duivesteyn/thepricedisplay-hardwaredesign/v2021/_hardware-specification/2.9inch-e-Paper-Module-B-details-size.jpg

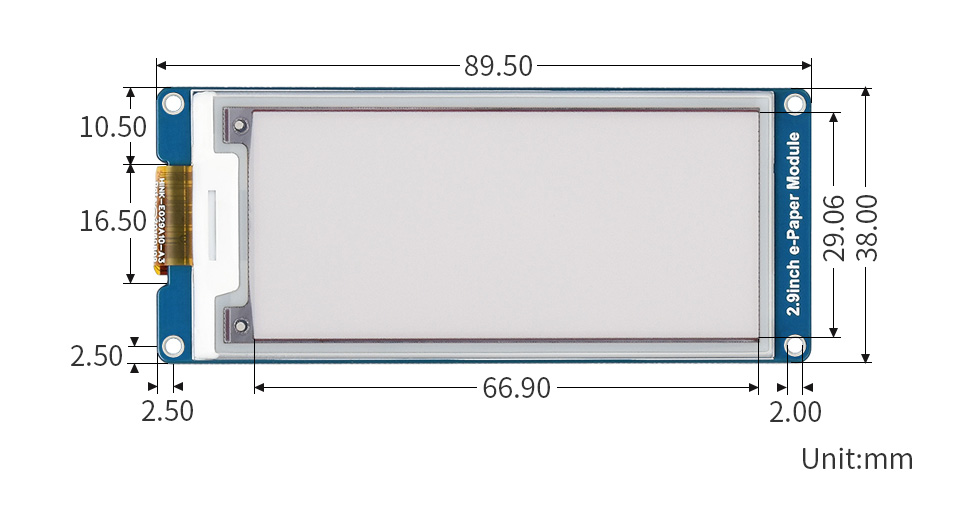
v2021/_hardware-specification/2.9inch-e-Paper-Module-B-details-size.jpg
