duivesteyn/thepricedisplay-hardwaredesign/v2021/_photos/2021-06-27 IMG151400_mainscreencomplete.jpg

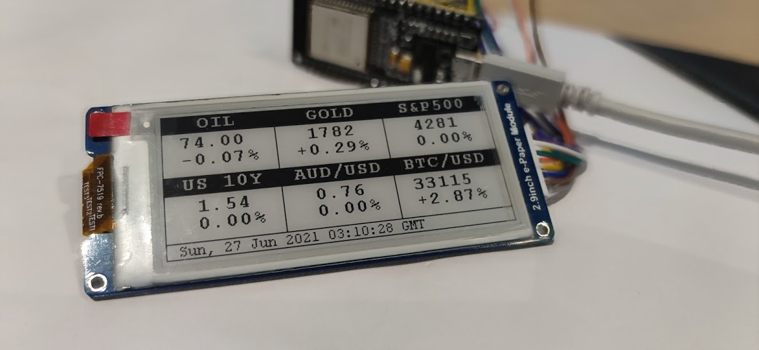
v2021/_photos/2021-06-27 IMG151400_mainscreencomplete.jpg
