duivesteyn/thepricedisplay-hardwaredesign/v2021/_photos/image (1).png

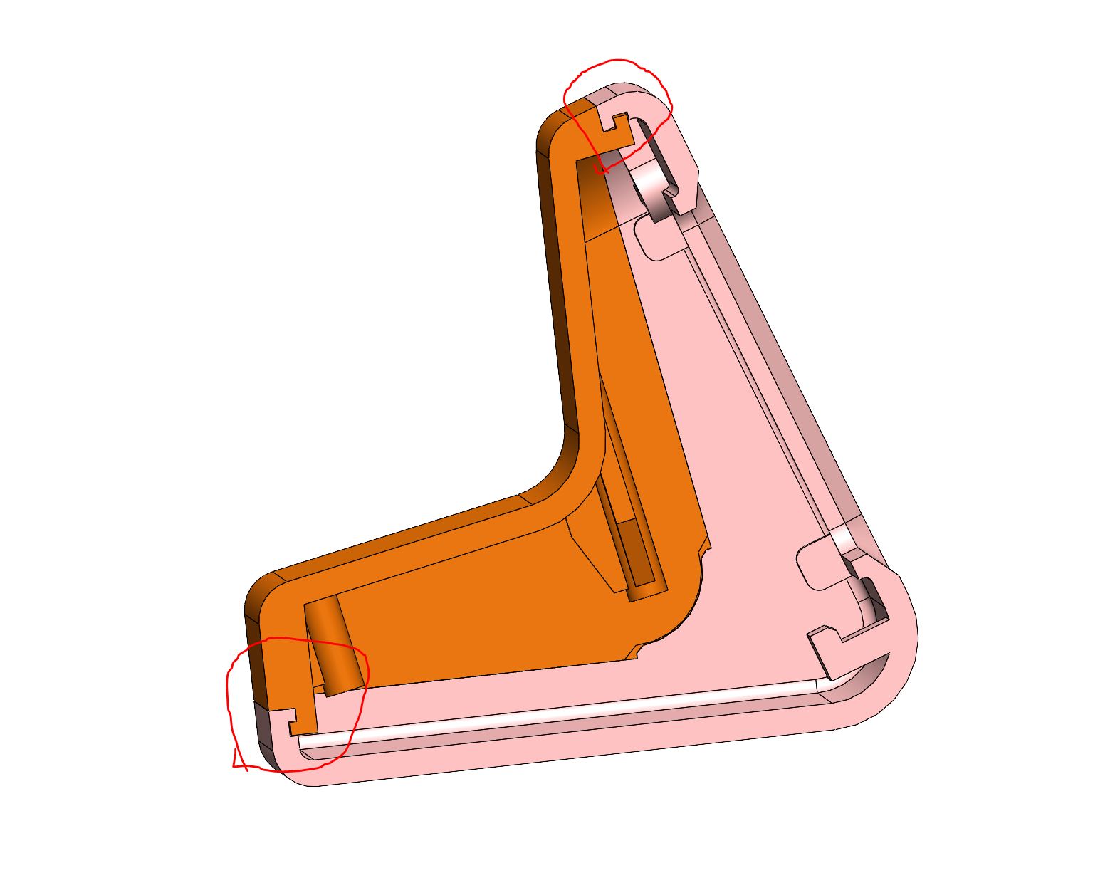
v2021/_photos/image (1).png
