duivesteyn/thepricedisplay-hardwaredesign/v2021/_photos/image (2).png

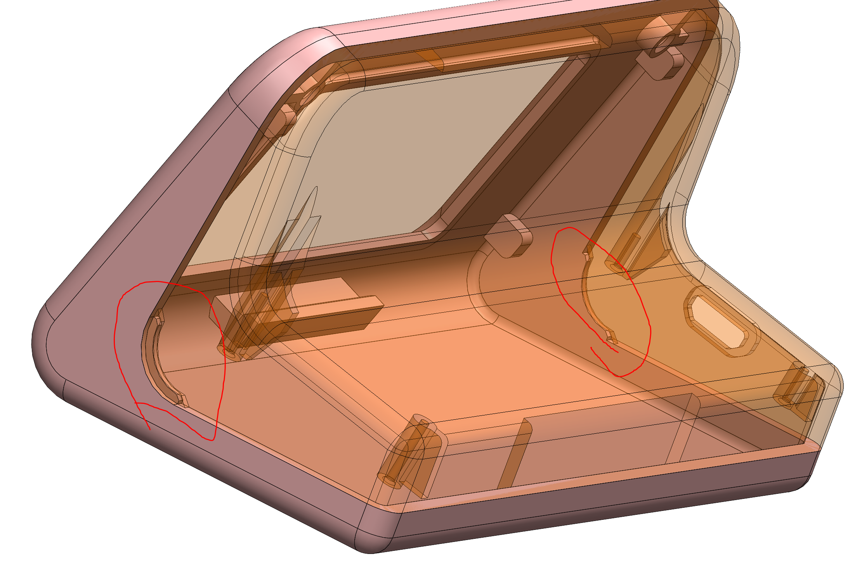
v2021/_photos/image (2).png
