duivesteyn/thepricedisplay-hardwaredesign/v2021/_photos/image (3).png

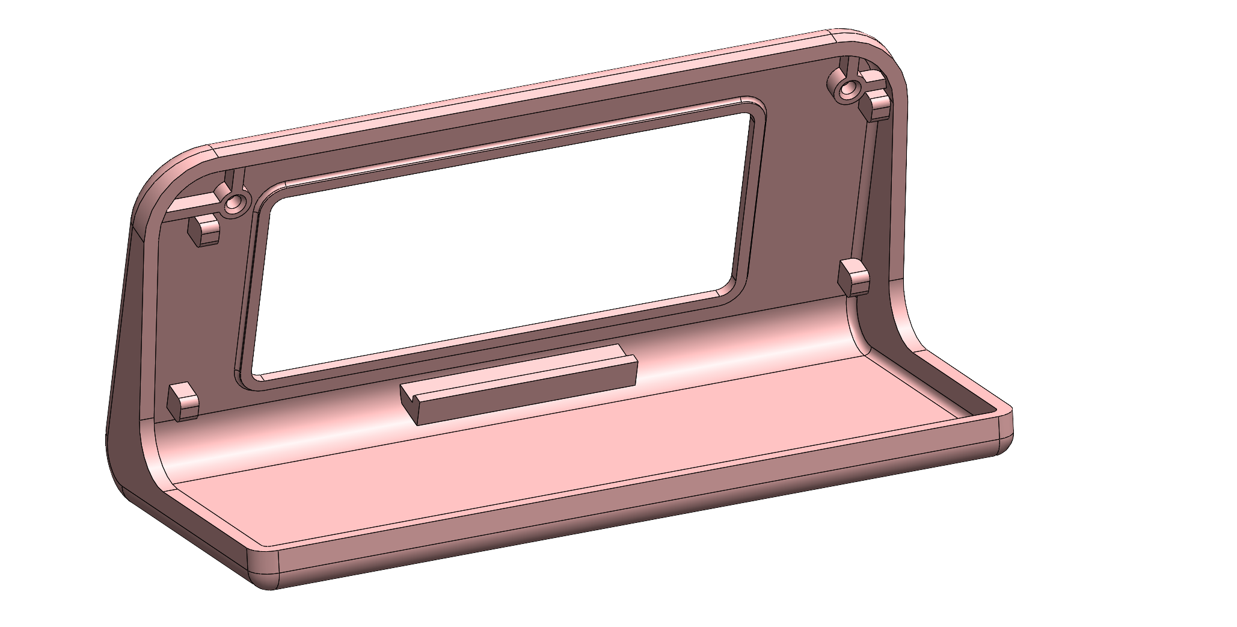
v2021/_photos/image (3).png
