duivesteyn/thepricedisplay-hardwaredesign/v2021/_photos/image (4).png

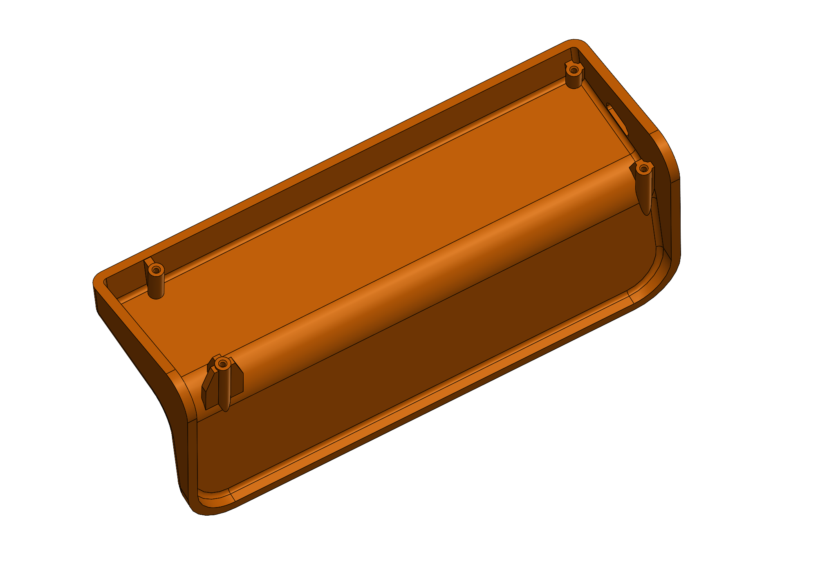
v2021/_photos/image (4).png
