duivesteyn/thepricedisplay-hardwaredesign/v2021/_photos/image (5).png

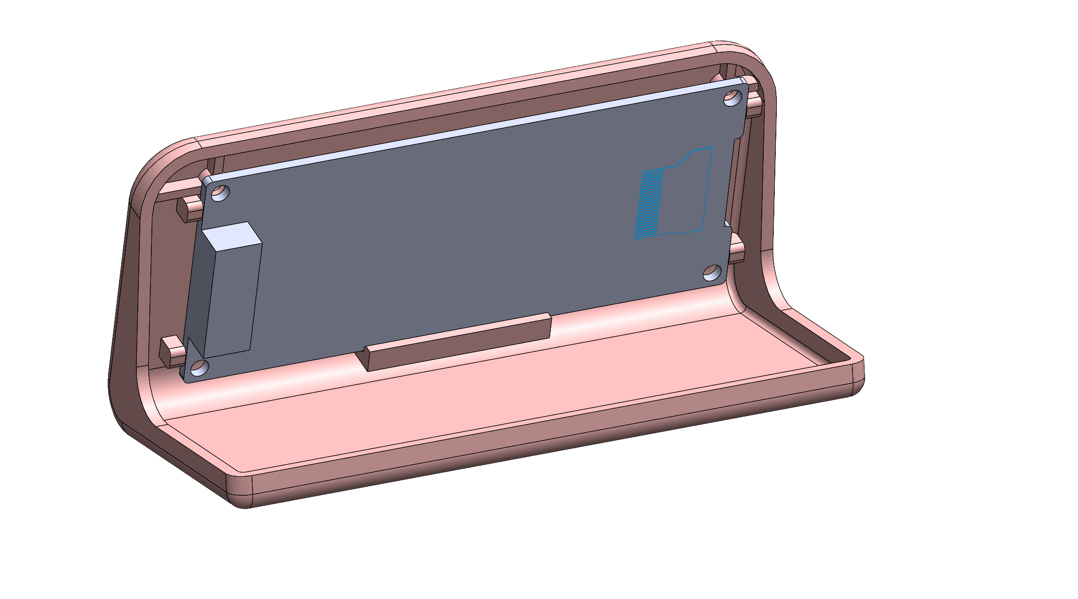
v2021/_photos/image (5).png
