duivesteyn/thepricedisplay-hardwaredesign/v2021/_photos/image (6).png

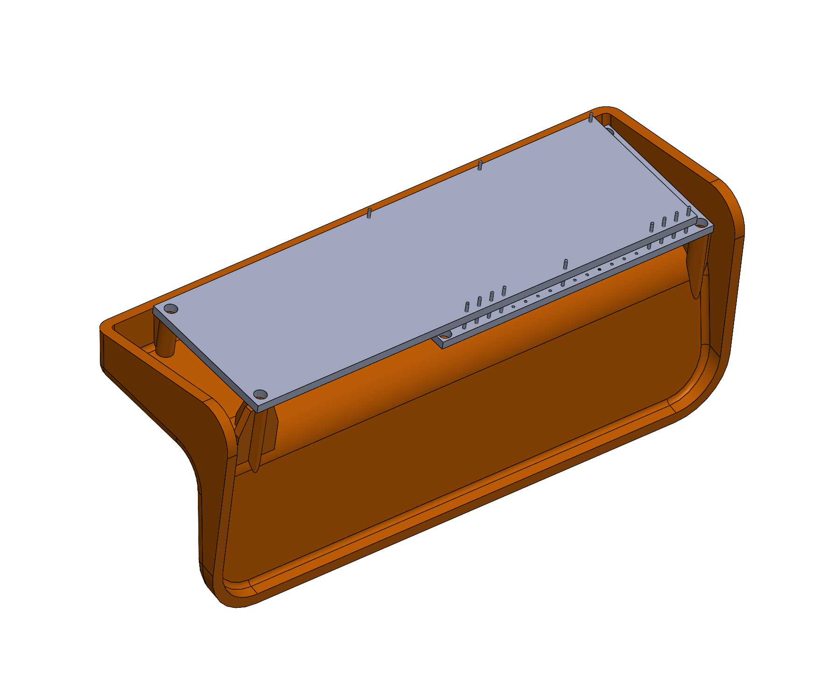
v2021/_photos/image (6).png
