duivesteyn/thepricedisplay-hardwaredesign/v2021/_photos/image (7).png

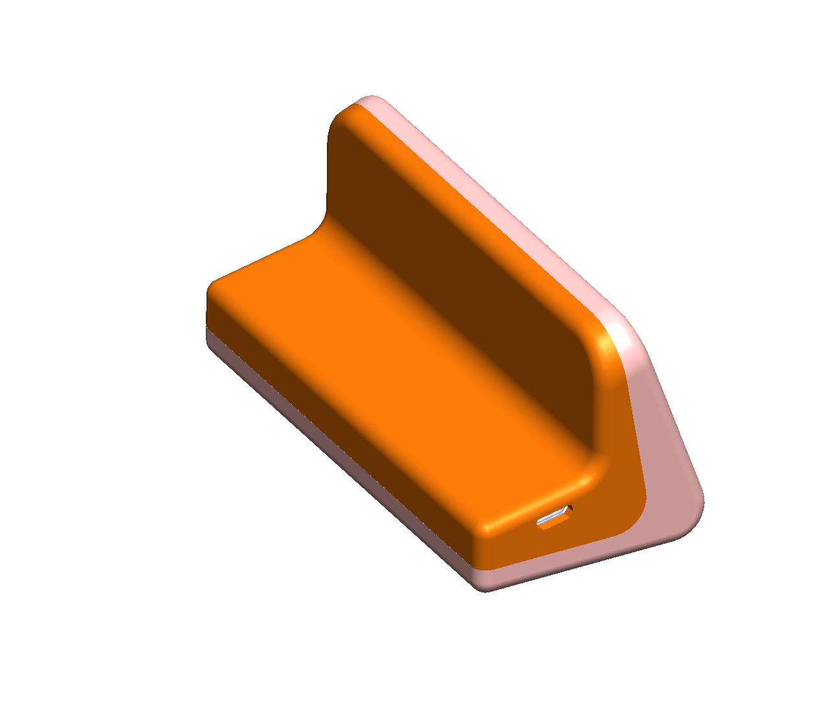
v2021/_photos/image (7).png
