duivesteyn/thepricedisplay-hardwaredesign/v2021/_photos/image (8).png

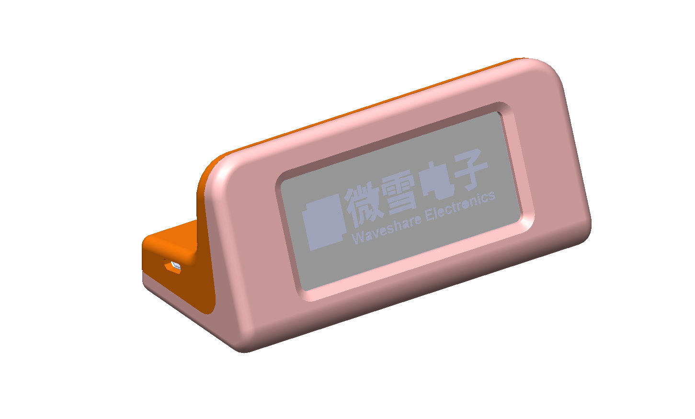
v2021/_photos/image (8).png
