duivesteyn/thepricedisplay-hardwaredesign/v2021/_photos/image.png

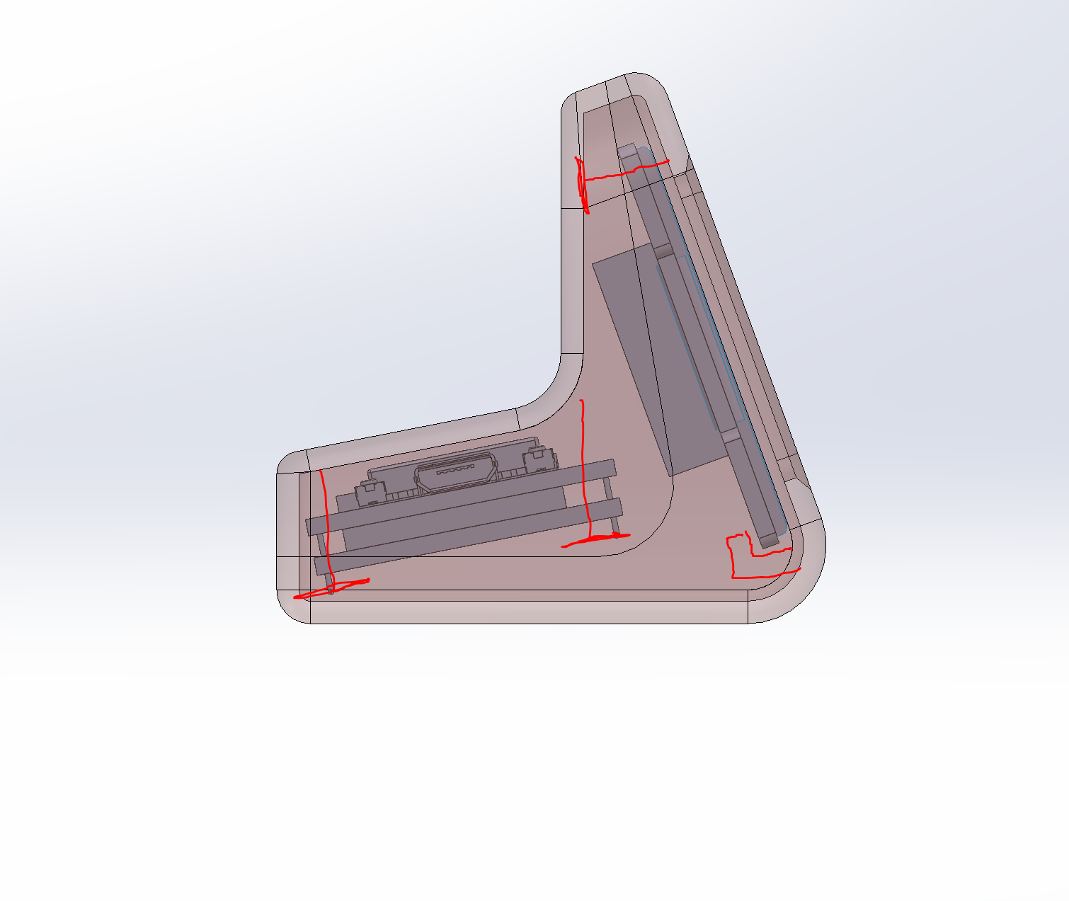
v2021/_photos/image.png
