duivesteyn/thepricedisplay-hardwaredesign/v2021/Case Design/_Screenshots/2021-10-26 Back Redesign - image (3).png

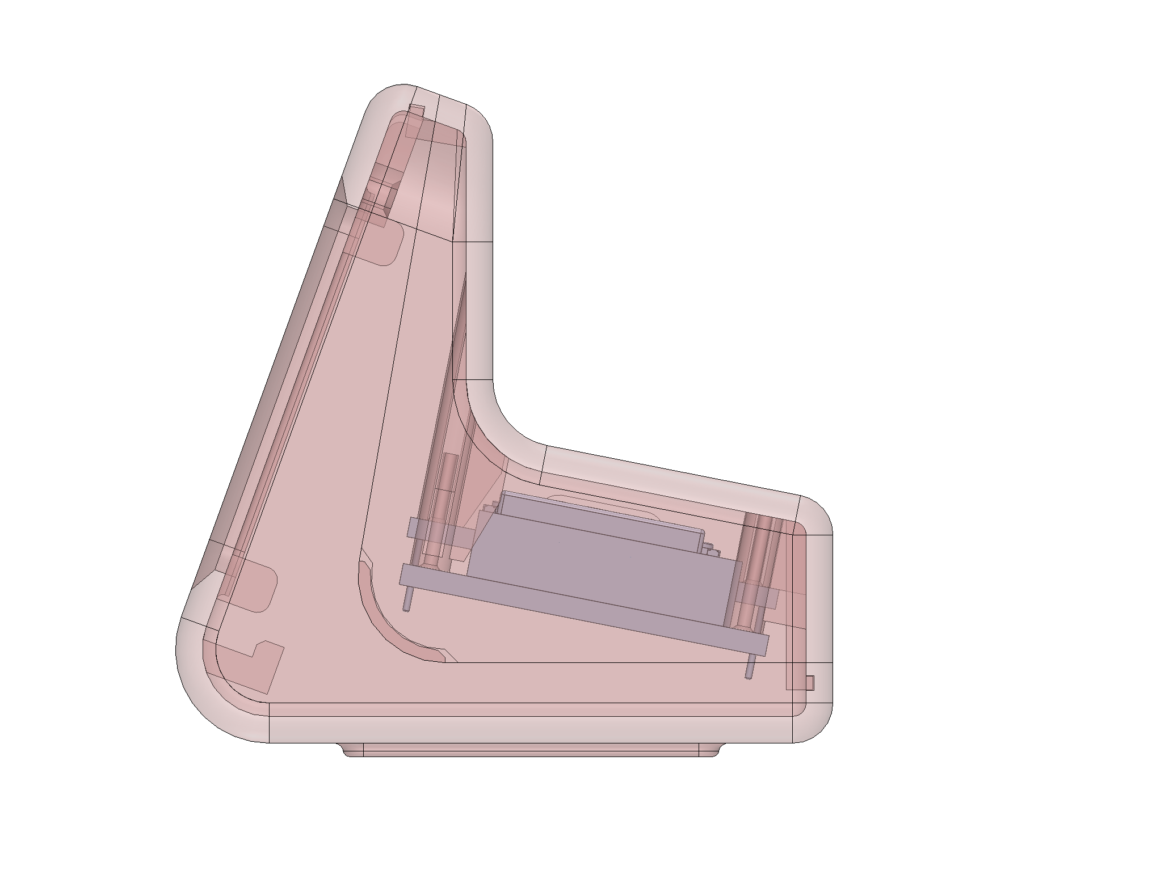
v2021/Case Design/_Screenshots/2021-10-26 Back Redesign - image (3).png
