duivesteyn/thepricedisplay-hardwaredesign/v2021/PCB Design/ver 0.4/03 Screenshots of Final/pcb-2021-rev4-3s.png

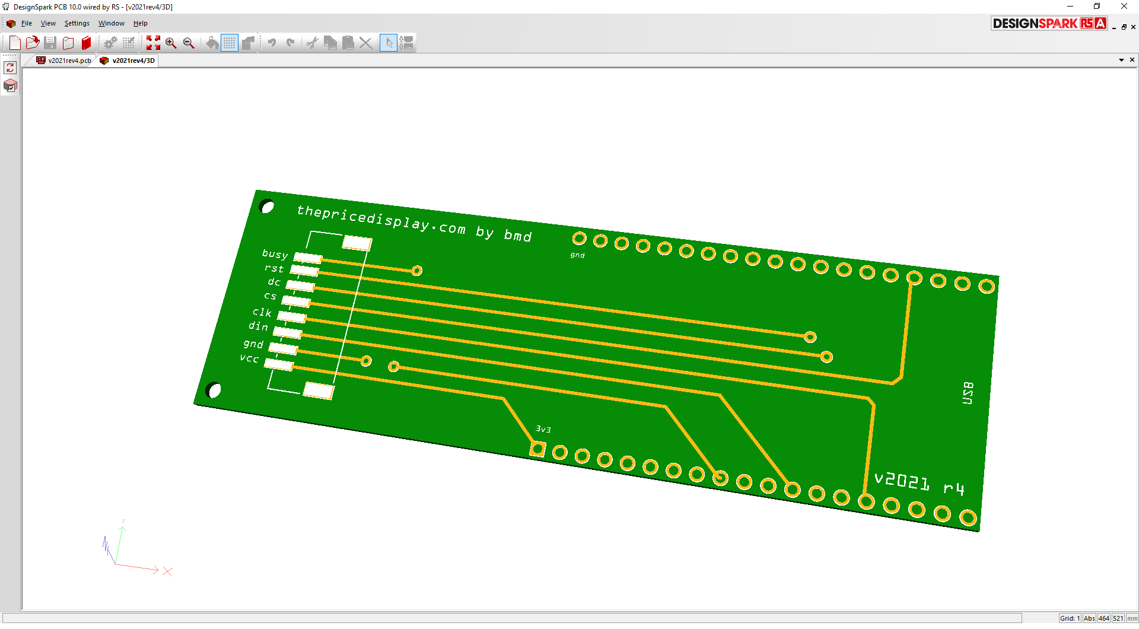
v2021/PCB Design/ver 0.4/03 Screenshots of Final/pcb-2021-rev4-3s.png
