duivesteyn/thepricedisplay-hardwaredesign/v2021/Case Design/_parts/mycustompcb/Screenshot (17).png

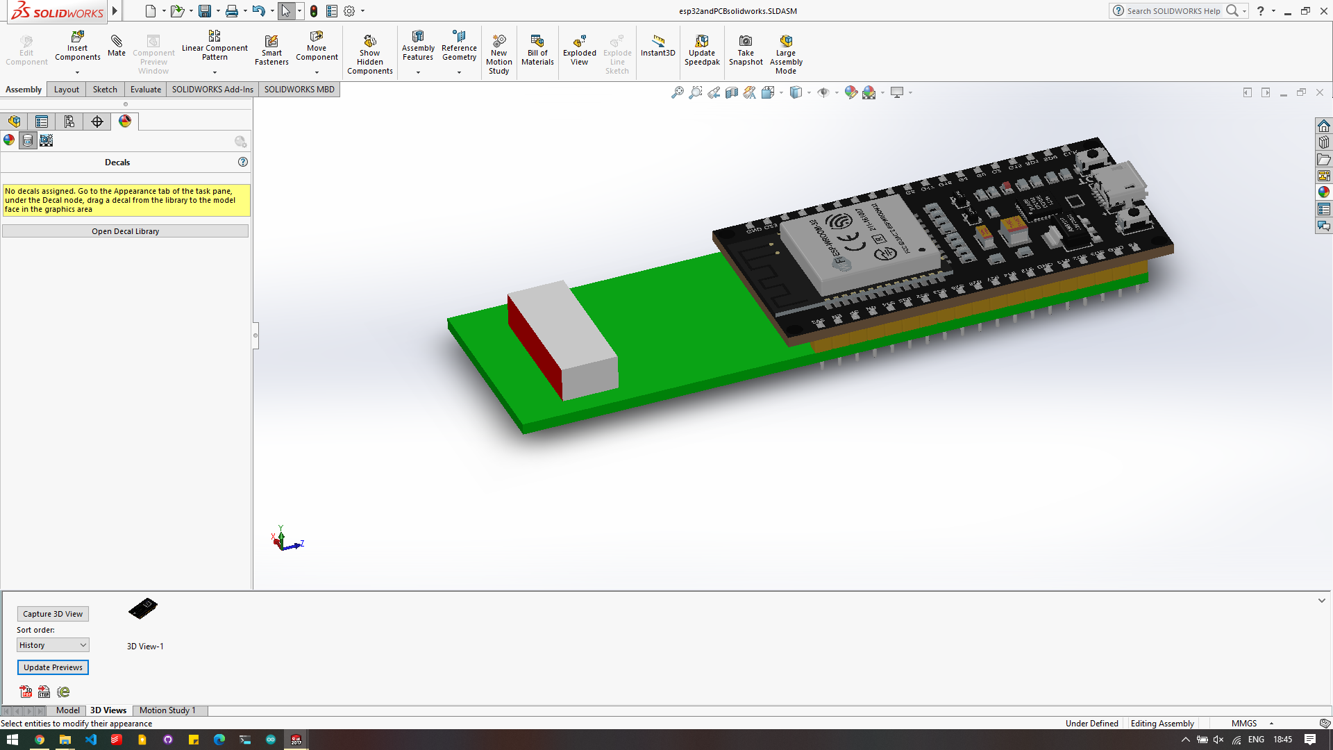
v2021/Case Design/_parts/mycustompcb/Screenshot (17).png
