duivesteyn/thepricedisplay-hardwaredesign/v2021/PCB Design/ver 0.1/02 PDF Export/v2021-1_etch_mask_top_mirror.pdf

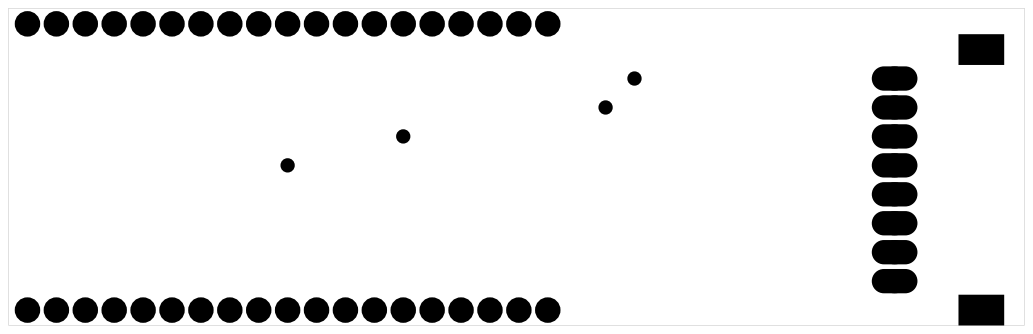
[picture p50: page 1]
