duivesteyn/thepricedisplay-hardwaredesign/v2021/PCB Design/ver 0.1/02 PDF Export/v2021-1_etch_silk_bottom.pdf

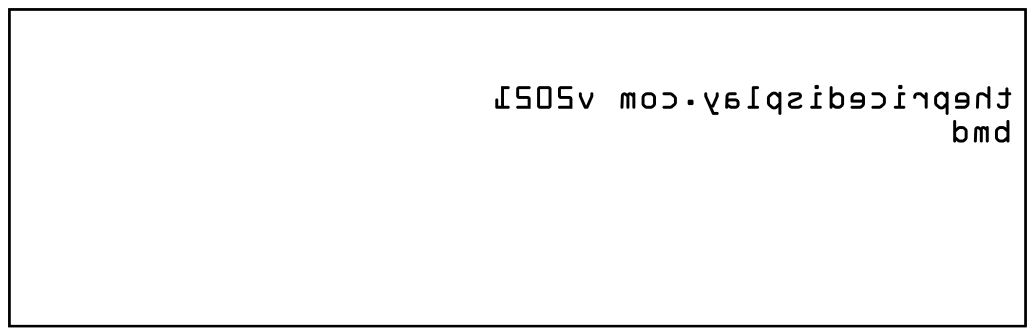
[picture p51: page 1]
