duivesteyn/thepricedisplay-hardwaredesign/v2021/PCB Design/ver 0.1/02 PDF Export/v2021-1_etch_silk_bottom_mirror.pdf

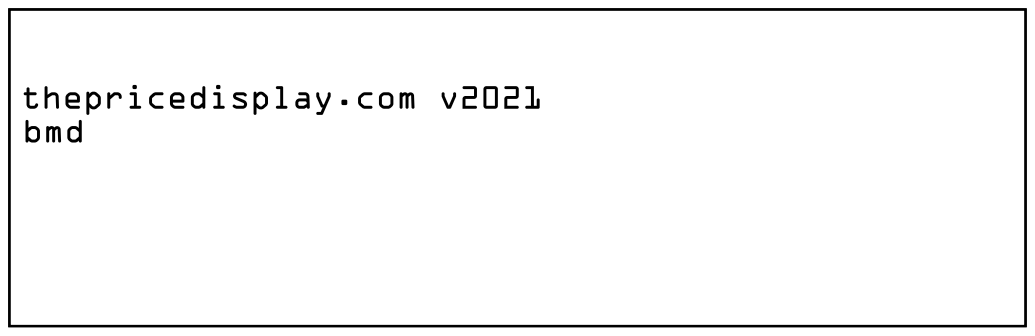
[picture p52: page 1]
